bitmorse/specklesensor/docs/figures/eval/snr.png

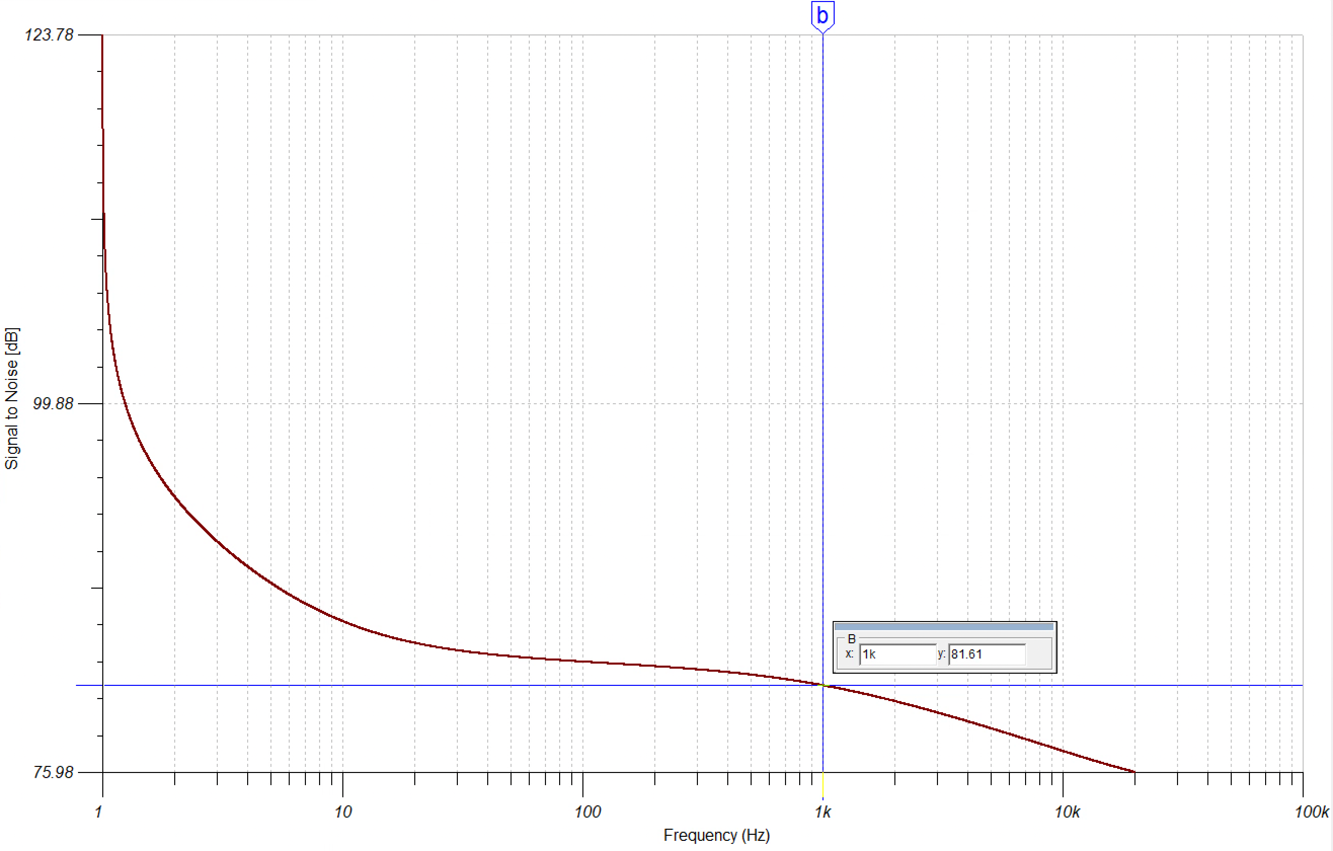
docs/figures/eval/snr.png
