bitmorse/specklesensor/docs/figures/impl/guardring.png

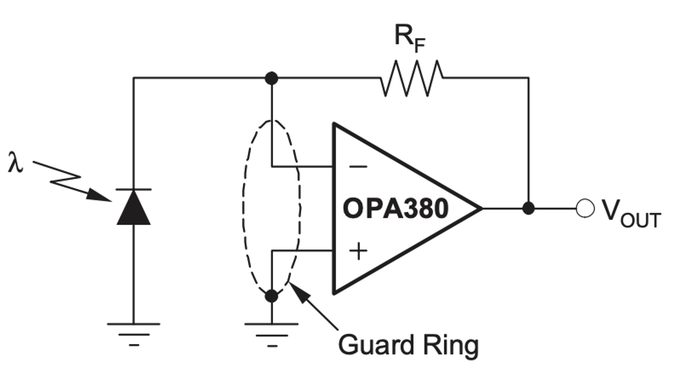
docs/figures/impl/guardring.png
